JaafarRammal/FPGA_Year1_Project/Full_Frame_in_game_720pi/out1.jpg

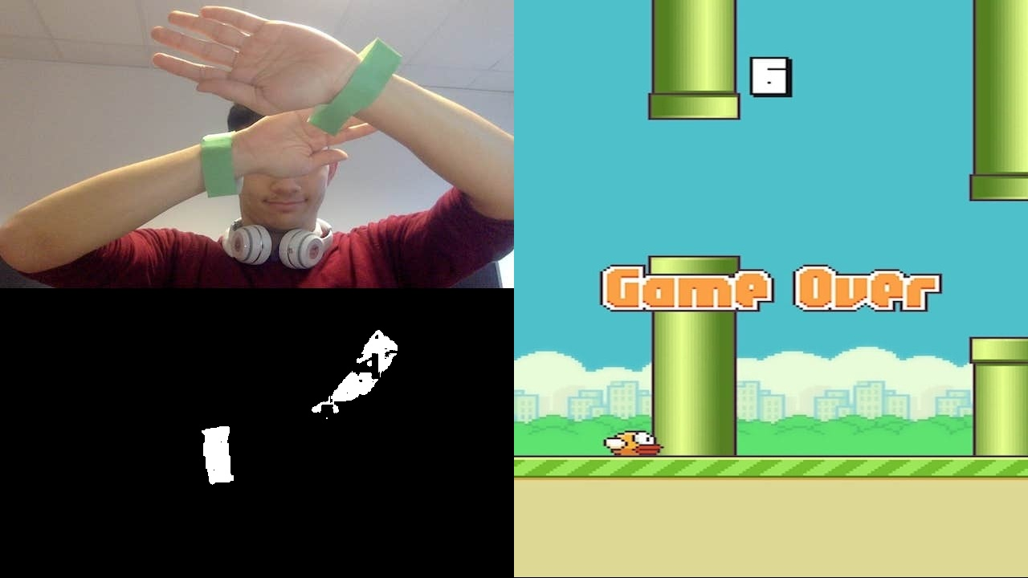
Full_Frame_in_game_720pi/out1.jpg
