JaafarRammal/FPGA_Year1_Project/Full_Frame_CV2_1080pi/out1.jpg

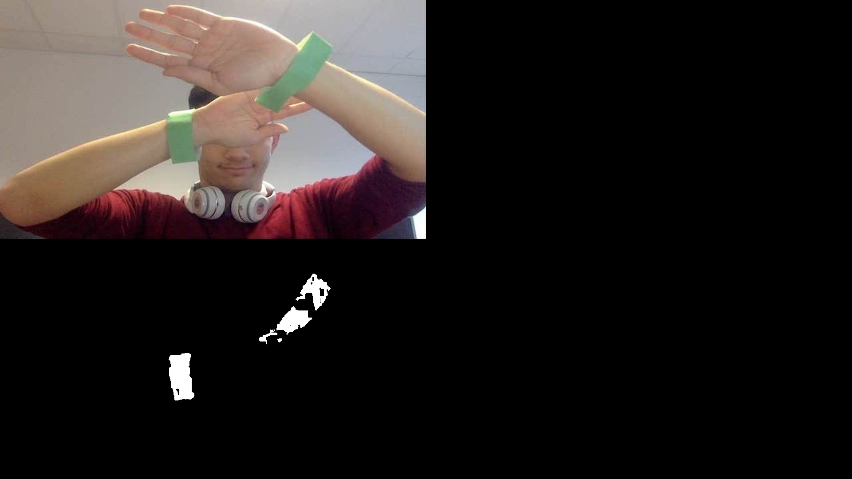
Full_Frame_CV2_1080pi/out1.jpg
