JaafarRammal/FPGA_Year1_Project/Python Game/assets/background-day.png

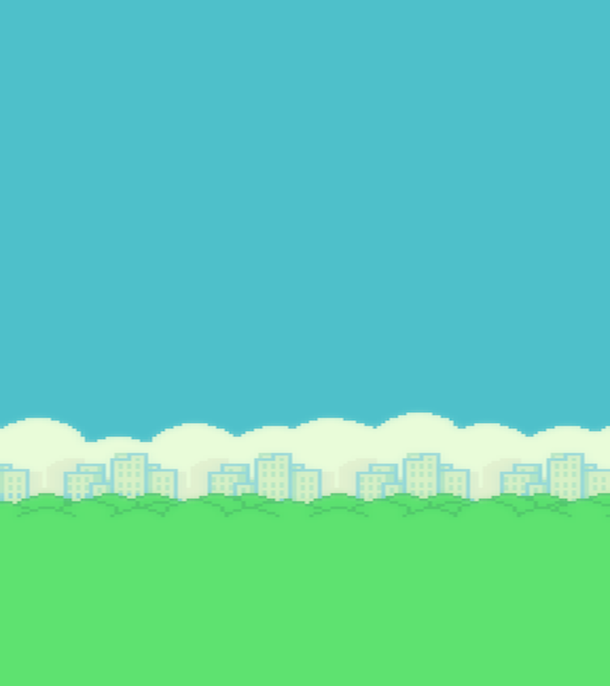
Python Game/assets/background-day.png
