JaafarRammal/FPGA_Year1_Project/Python Game/assets/background-night.png

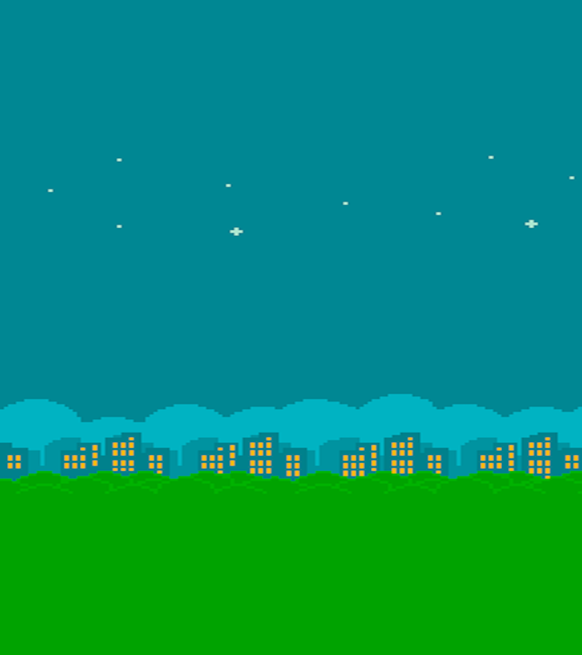
Python Game/assets/background-night.png
